PhilMo6/HEPA-Positive-Pressure-Hood/bagAddapter/input/bagRingLarge.stl

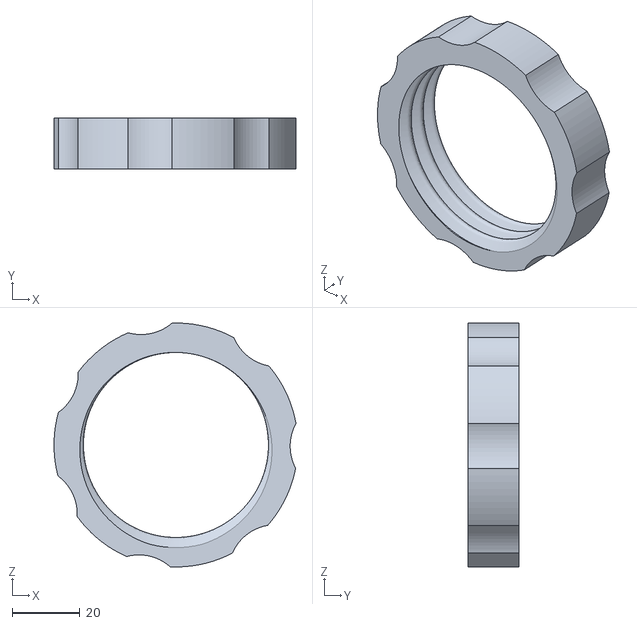
[picture p19: CAD file, 2020-03-22]
bagAddapter/input/bagRingLarge.stl
71.4 x 15.0 x 72.0
