PhilMo6/HEPA-Positive-Pressure-Hood/bagAddapter/outputValve/bagAddapterOutput.stl

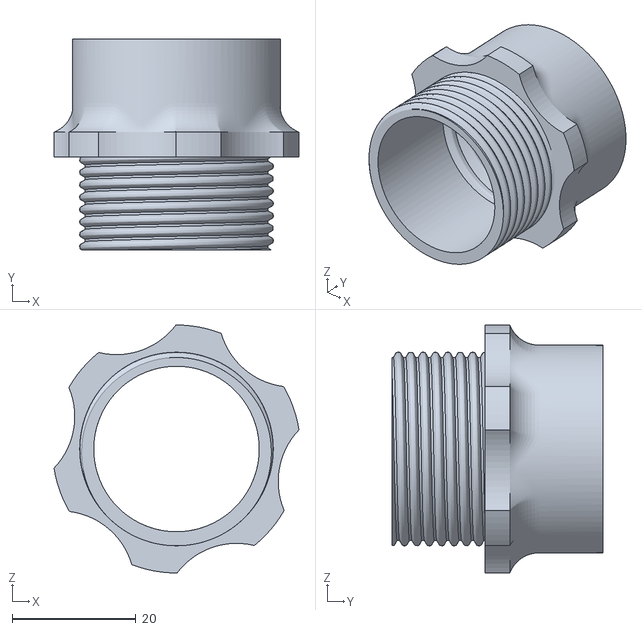
[picture p20: CAD file, 2020-03-23]
bagAddapter/outputValve/bagAddapterOutput.stl
39.5 x 34.0 x 40.0
