PhilMo6/HEPA-Positive-Pressure-Hood/maskAddapters/3mAngle.stl

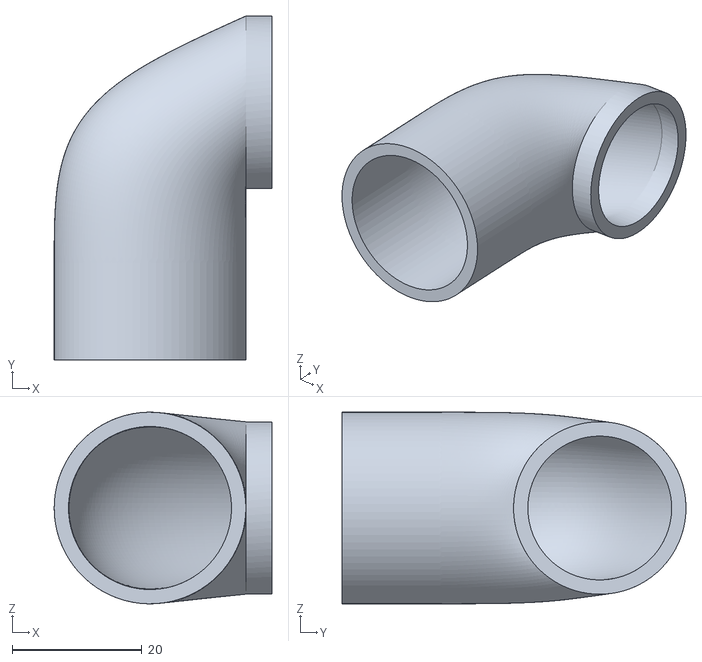
[picture p21: CAD file, 2020-03-22]
maskAddapters/3mAngle.stl
33.5 x 53.0 x 29.5
