PhilMo6/HEPA-Positive-Pressure-Hood/12v/fanCoverFlat.stl

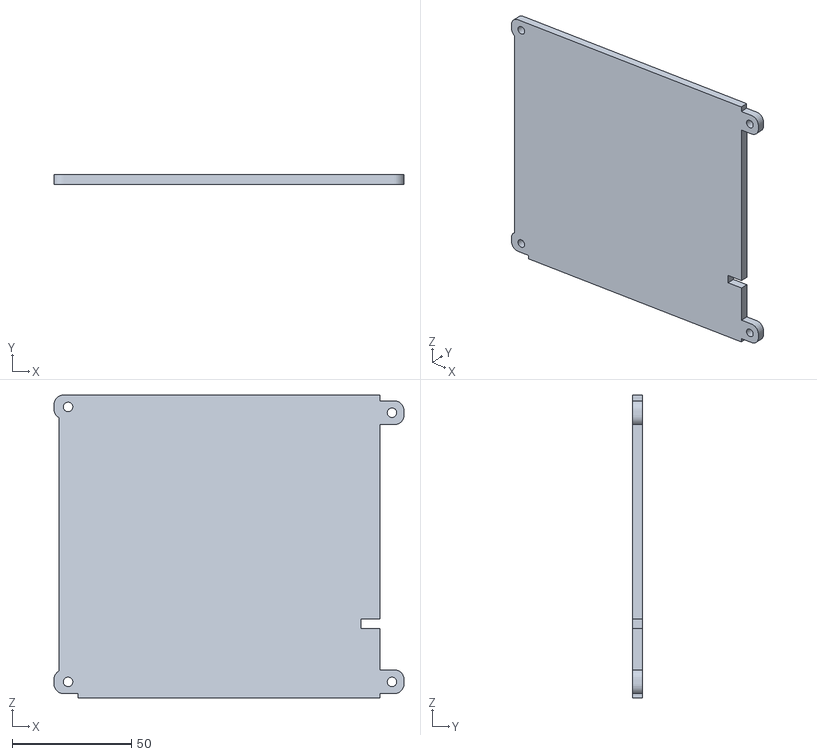
[picture p22: CAD file, 2020-03-22]
12v/fanCoverFlat.stl
146.9 x 4.00 x 127.2
