PhilMo6/HEPA-Positive-Pressure-Hood/5v/filterCover.stl

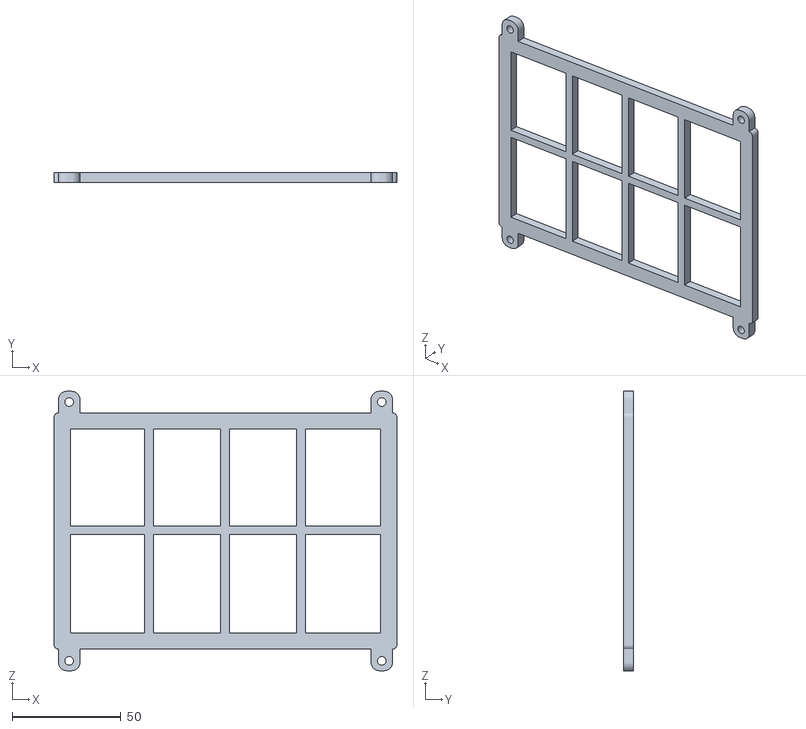
[picture p23: CAD file, 2020-03-22]
5v/filterCover.stl
158.0 x 4.50 x 128.8
