PhilMo6/HEPA-Positive-Pressure-Hood/bagAddapter/input/bagAddapterInputLarge.stl

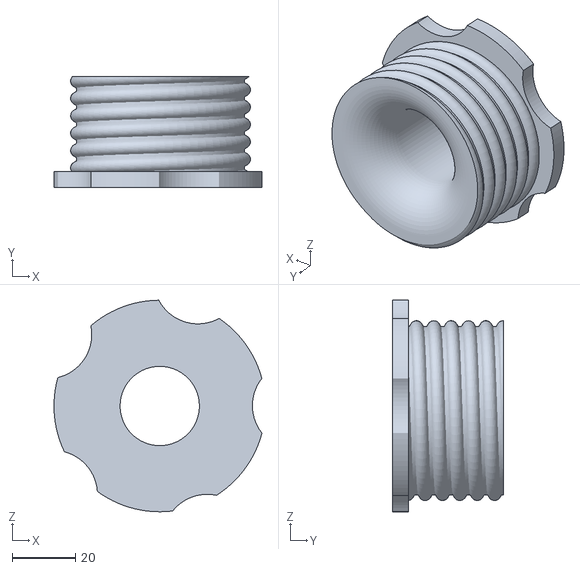
[picture p24: CAD file, 2020-03-22]
bagAddapter/input/bagAddapterInputLarge.stl
65.9 x 35.0 x 67.0
