PhilMo6/HEPA-Positive-Pressure-Hood/maskAddapters/3mCoupler.stl

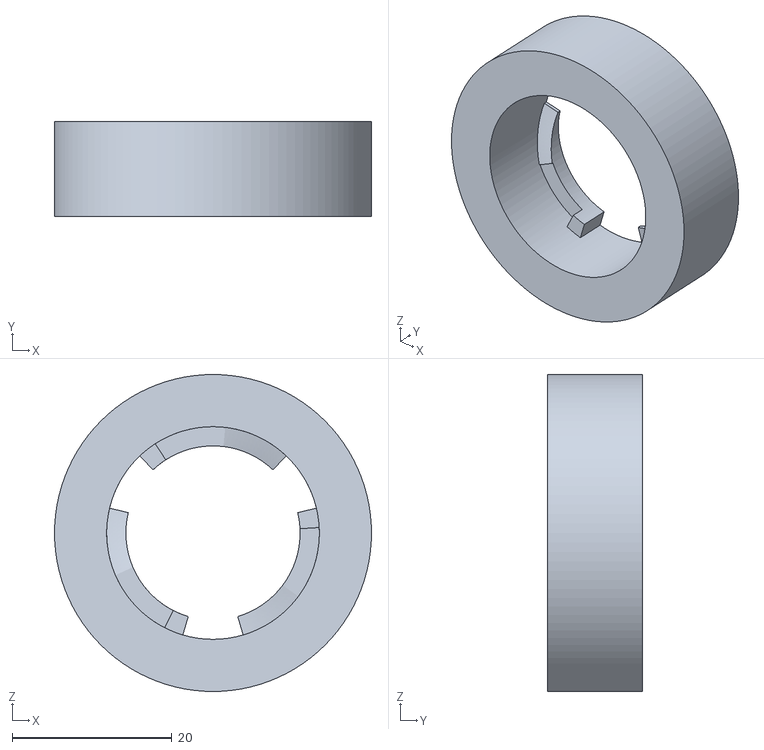
[picture p25: CAD file, 2020-03-22]
maskAddapters/3mCoupler.stl
39.8 x 11.9 x 39.8
